menloparkinnovation/menlo_gigatron/menlo_gigatron_de10_nano/silicon_shell/Reset_Delay.sv

module	Reset_Delay(iCLK,oRESET);
input		iCLK;
output reg	oRESET;
reg	[19:0]	Cont;

always@(posedge iCLK)
begin
	if(Cont != 20'hFFFFF)
	begin
		Cont	<=	Cont + 10'h1;
		oRESET	<=	1'b0;
	end
	else
	oRESET	<=	1'b1;
end

endmodule
