menloparkinnovation/menlo_gigatron/release_09092018/menlo_gigatron_de10_nano/vga_fifo_inst.v

vga_fifo	vga_fifo_inst (
	.data ( data_sig ),
	.rdclk ( rdclk_sig ),
	.rdreq ( rdreq_sig ),
	.wrclk ( wrclk_sig ),
	.wrreq ( wrreq_sig ),
	.q ( q_sig ),
	.rdempty ( rdempty_sig ),
	.wrfull ( wrfull_sig )
	);
